antmicro/data-center-dram-tester/assets/previews/layer0.webp

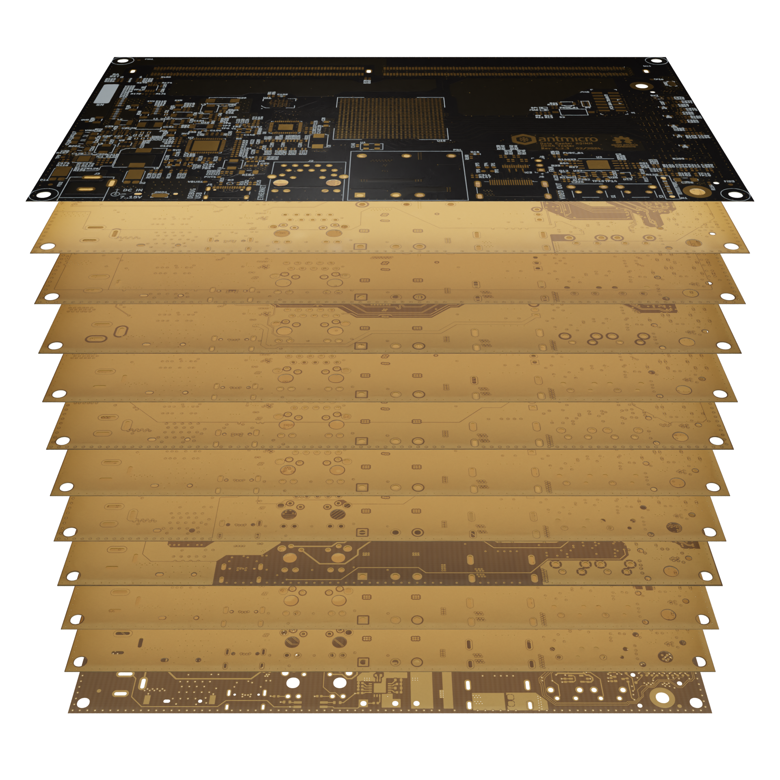
assets/previews/layer0.webp
