antmicro/data-center-dram-tester/assets/previews/layer1.webp

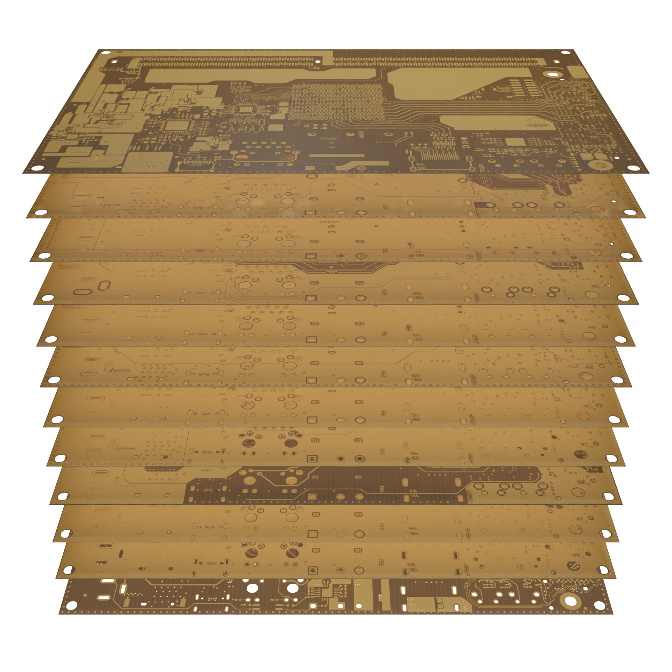
assets/previews/layer1.webp
