antmicro/data-center-dram-tester/assets/previews/layer2.webp

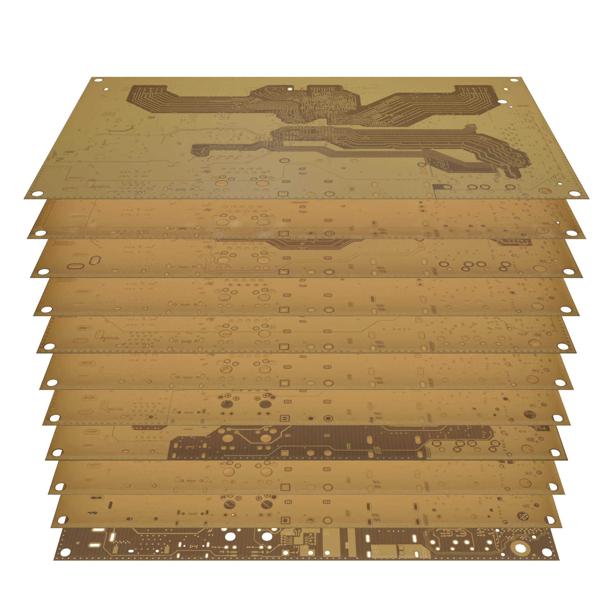
assets/previews/layer2.webp
