antmicro/data-center-dram-tester/assets/previews/layer3_thumbnail.png

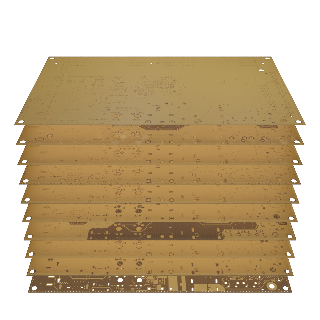
assets/previews/layer3_thumbnail.png
