antmicro/data-center-dram-tester/assets/previews/layer4.png

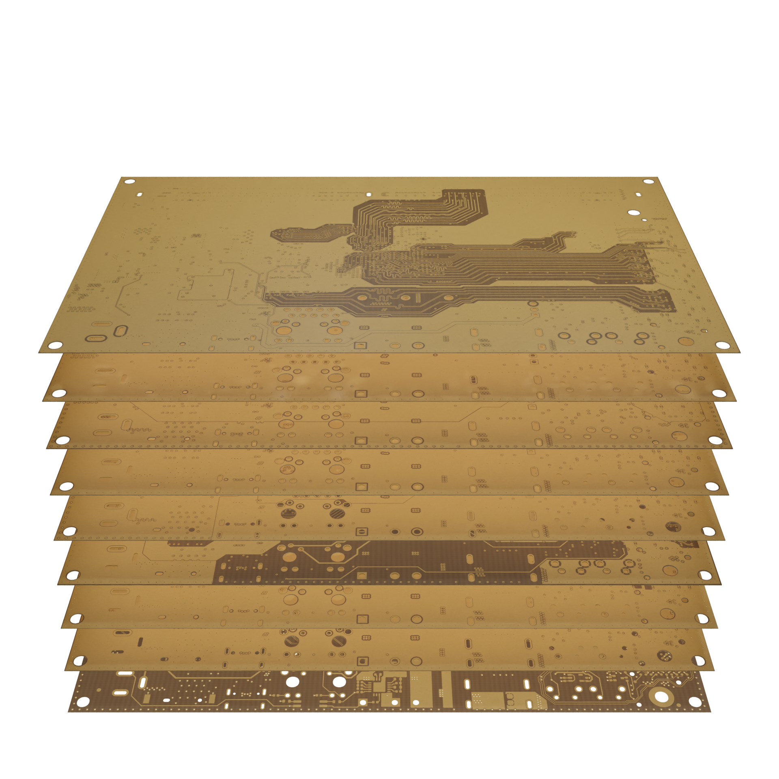
assets/previews/layer4.png
