antmicro/data-center-dram-tester/assets/previews/layer4_thumbnail.png

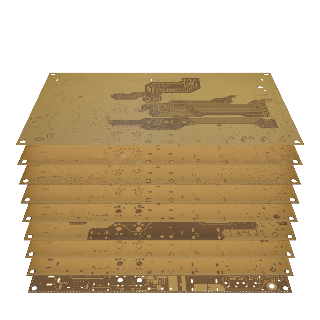
assets/previews/layer4_thumbnail.png
