antmicro/data-center-dram-tester/assets/previews/layer5.png

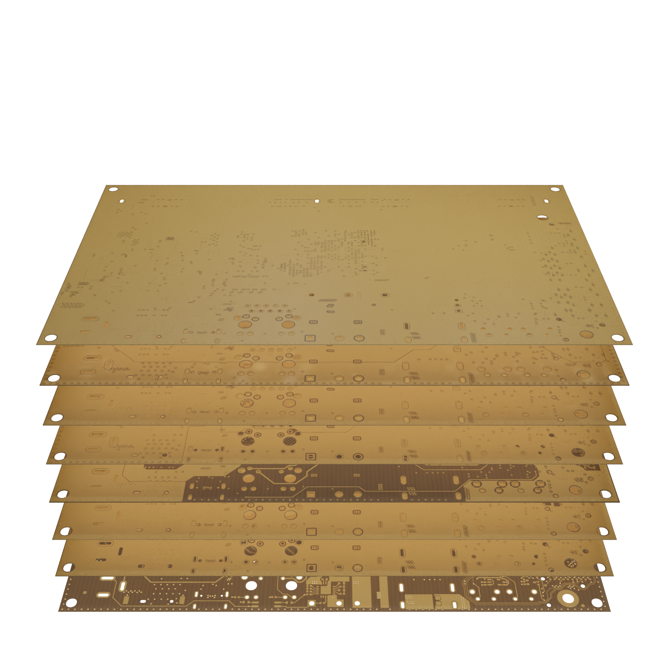
assets/previews/layer5.png
