antmicro/data-center-dram-tester/assets/previews/layer7.png

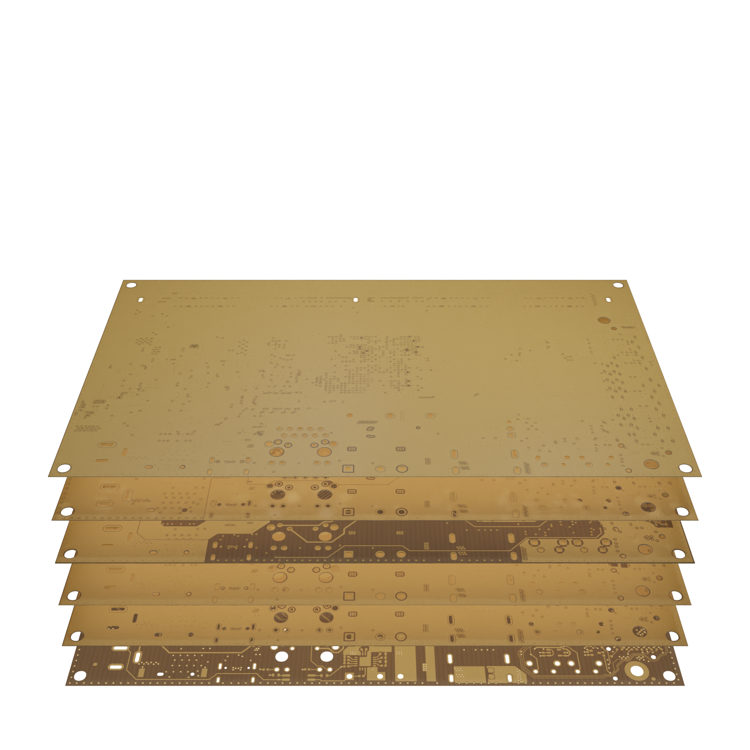
assets/previews/layer7.png
