antmicro/data-center-dram-tester/assets/previews/layer7_thumbnail.png

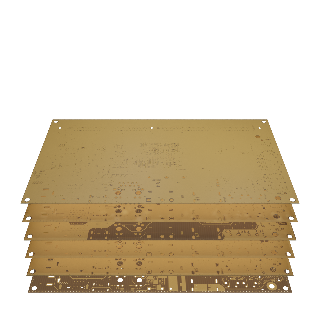
assets/previews/layer7_thumbnail.png
