antmicro/data-center-dram-tester/assets/previews/layer8.png

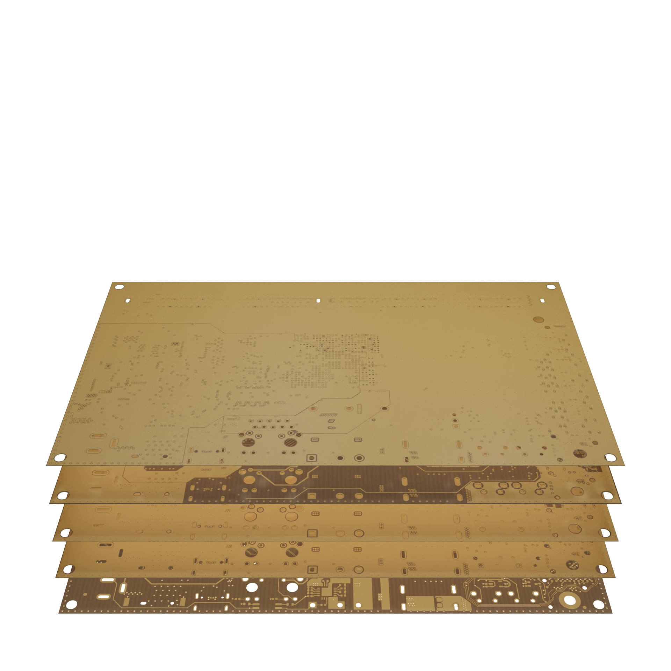
assets/previews/layer8.png
