antmicro/data-center-dram-tester/assets/previews/layer9.png

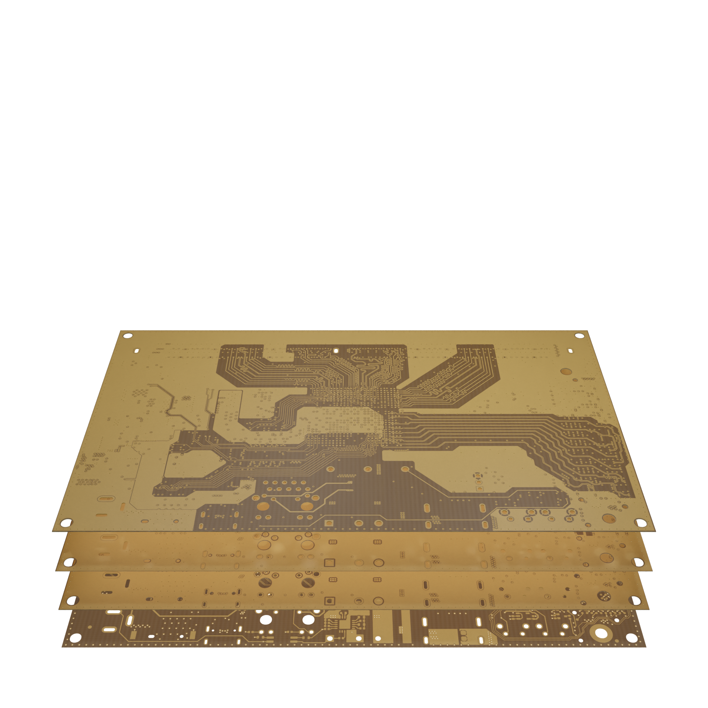
assets/previews/layer9.png
