antmicro/data-center-dram-tester/assets/previews/layer10.png

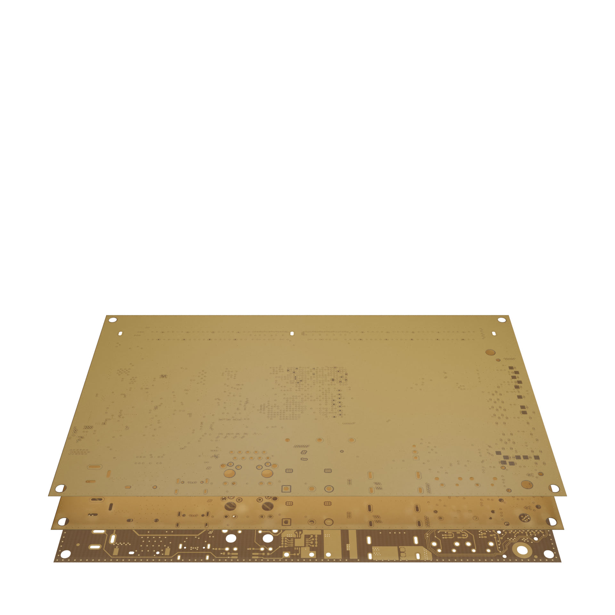
assets/previews/layer10.png
