antmicro/data-center-dram-tester/assets/previews/layer12.png

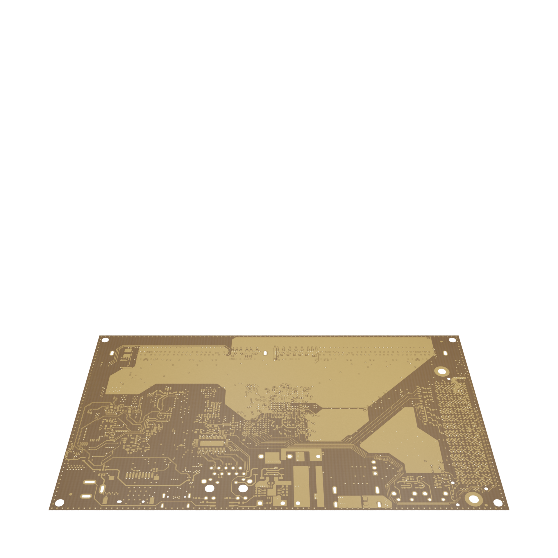
assets/previews/layer12.png
