antmicro/data-center-dram-tester/assets/previews/leftB.png

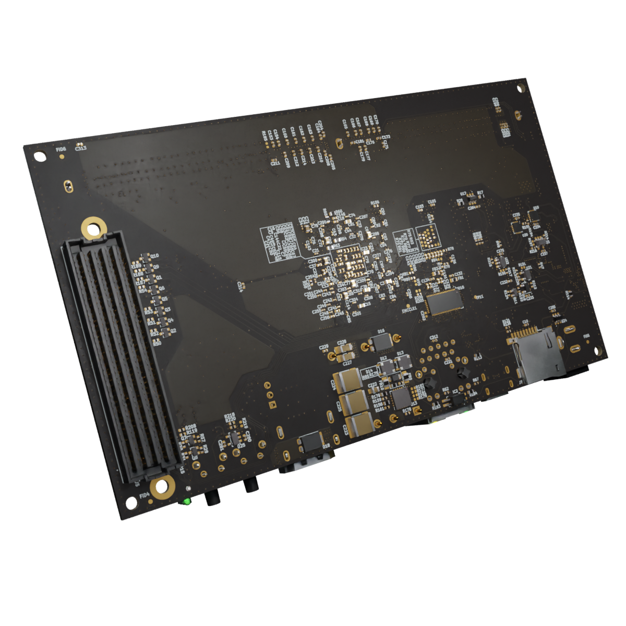
assets/previews/leftB.png
