antmicro/data-center-dram-tester/assets/previews/leftT.png

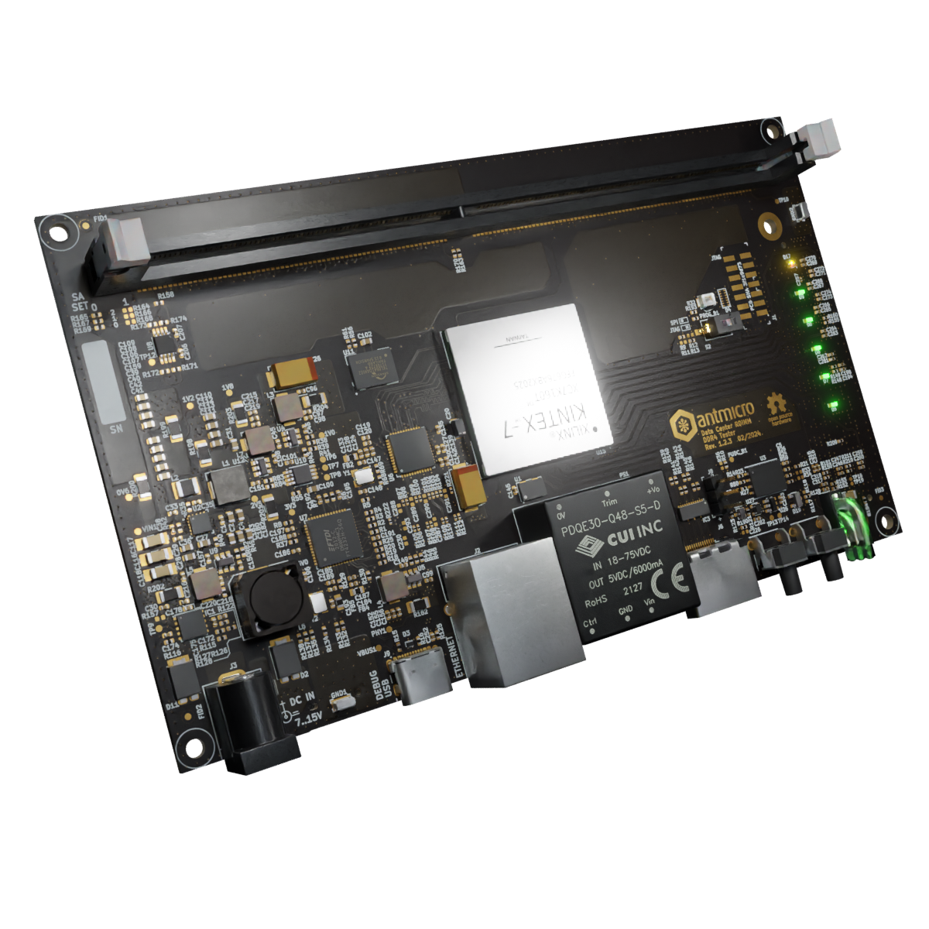
assets/previews/leftT.png
