antmicro/data-center-dram-tester/assets/previews/orthoB.png

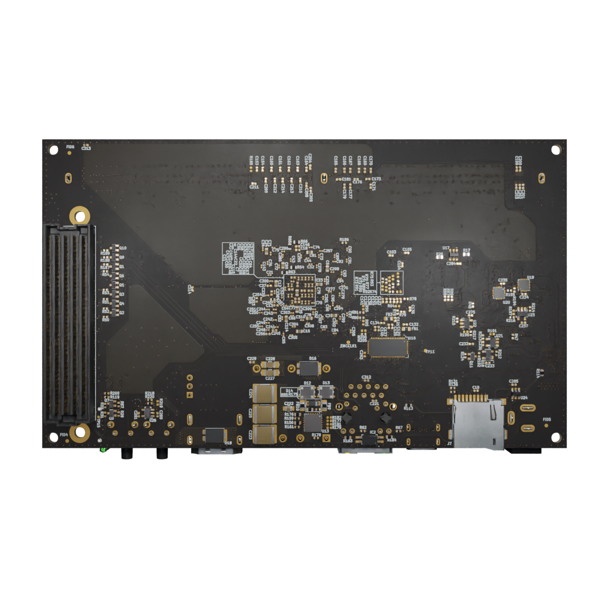
assets/previews/orthoB.png
