antmicro/data-center-dram-tester/assets/previews/orthoT.png

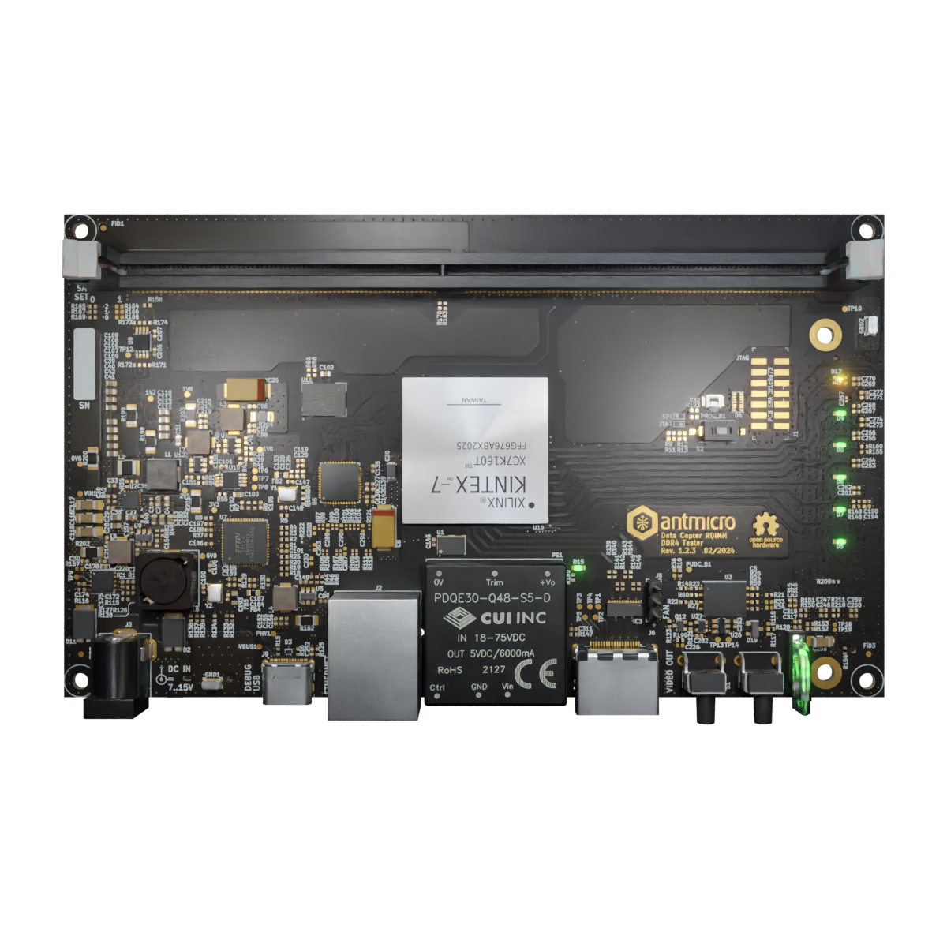
assets/previews/orthoT.png
