antmicro/data-center-dram-tester/assets/previews/photoB.png

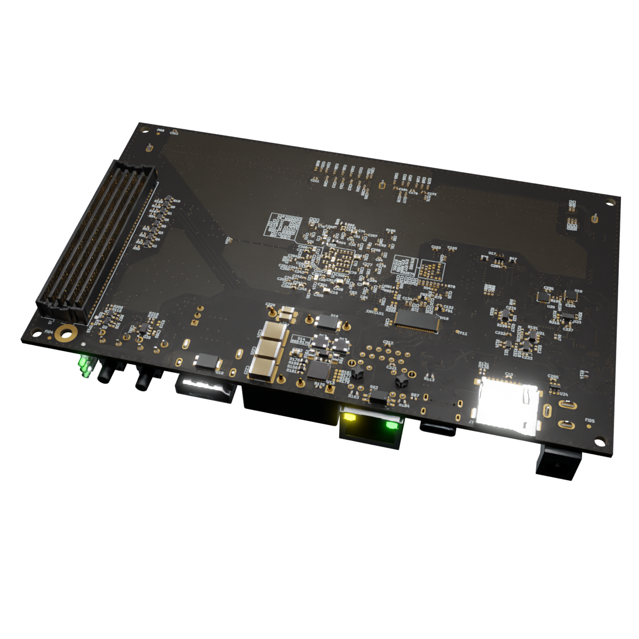
assets/previews/photoB.png
