antmicro/data-center-dram-tester/assets/previews/photoT.png

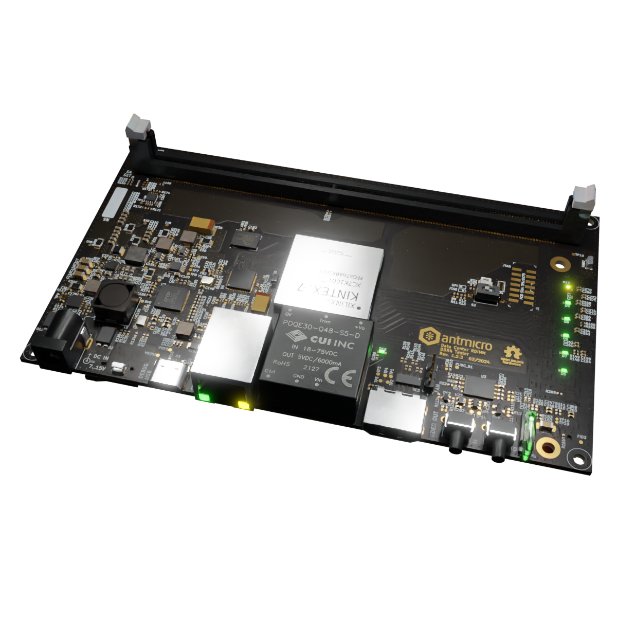
assets/previews/photoT.png
