antmicro/data-center-dram-tester/assets/previews/rightB.png

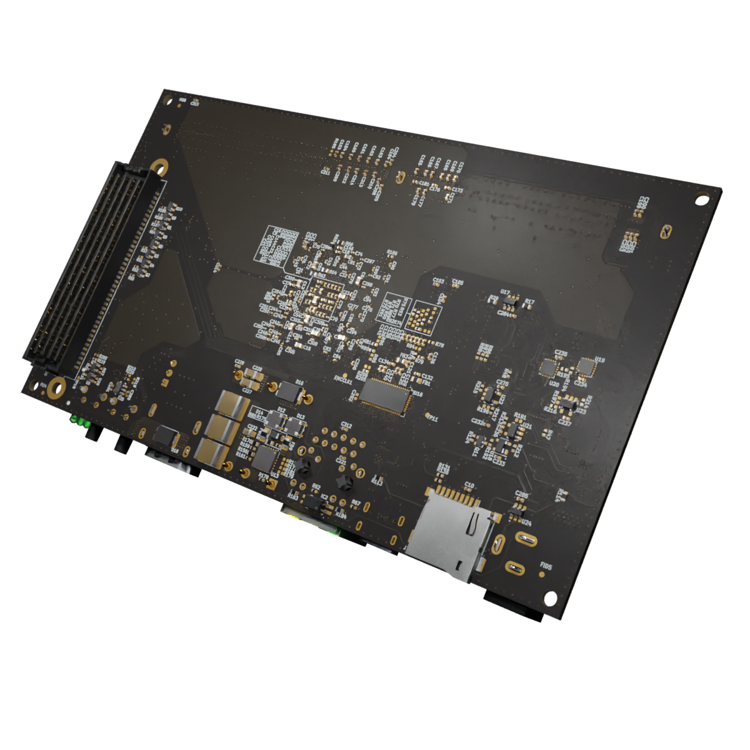
assets/previews/rightB.png
