antmicro/data-center-dram-tester/assets/previews/rightT.png

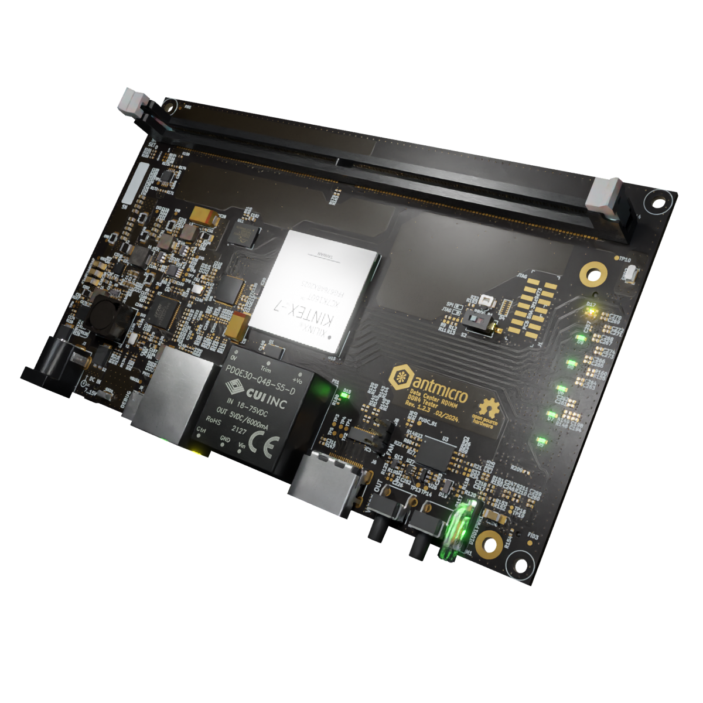
assets/previews/rightT.png
